MaskwaSam/GridMazePlatform/reference/photos/IMG_6221-preview.jpg

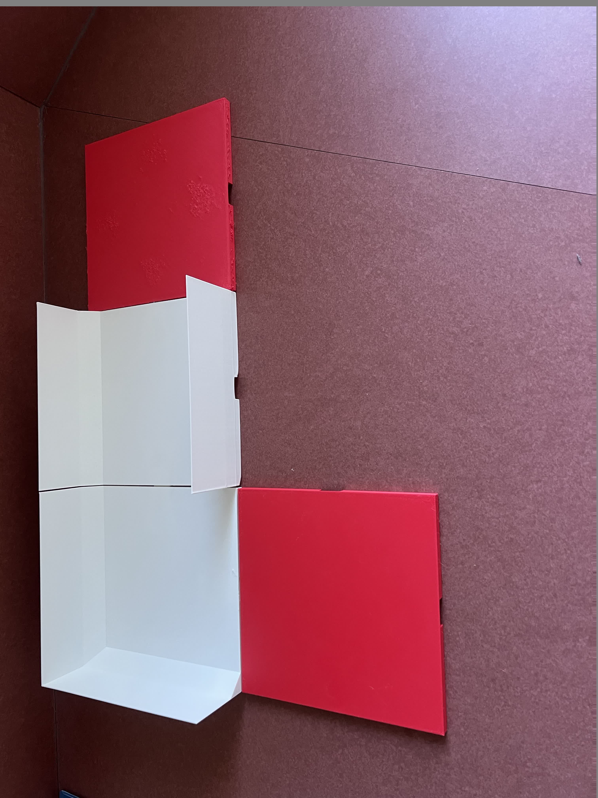
reference/photos/IMG_6221-preview.jpg
