MaskwaSam/GridMazePlatform/docs/images/h2d-wall-45deg-transition.png

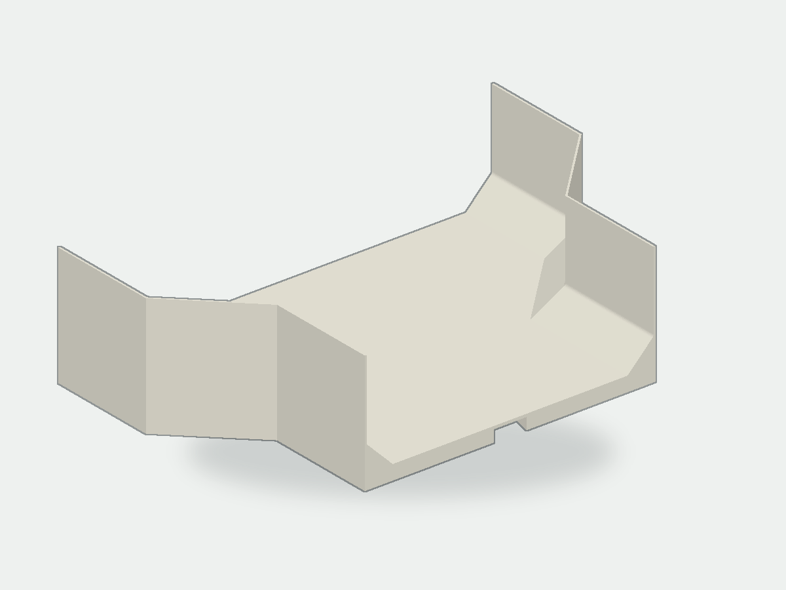
docs/images/h2d-wall-45deg-transition.png
