MaskwaSam/GridMazePlatform/docs/images/h2d-wall-200x300-end.png

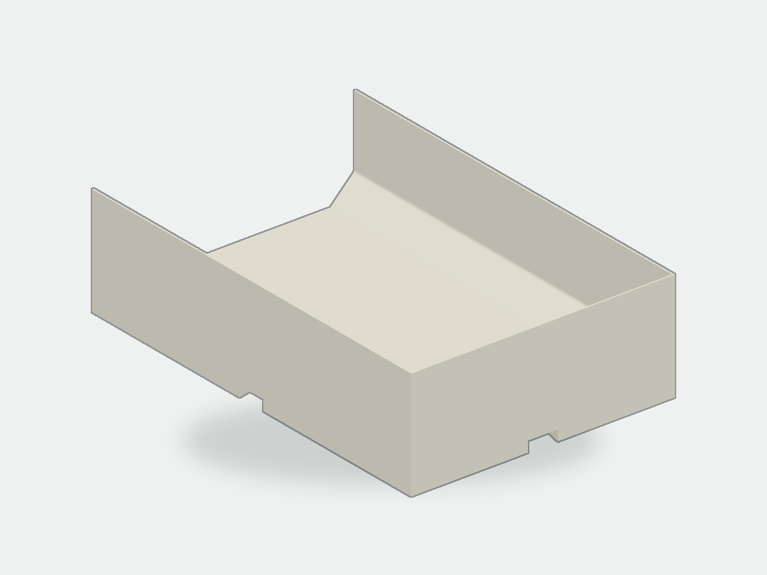
docs/images/h2d-wall-200x300-end.png
