MaskwaSam/GridMazePlatform/docs/images/h2d-wall-300x300-45deg-four-way-clean.png

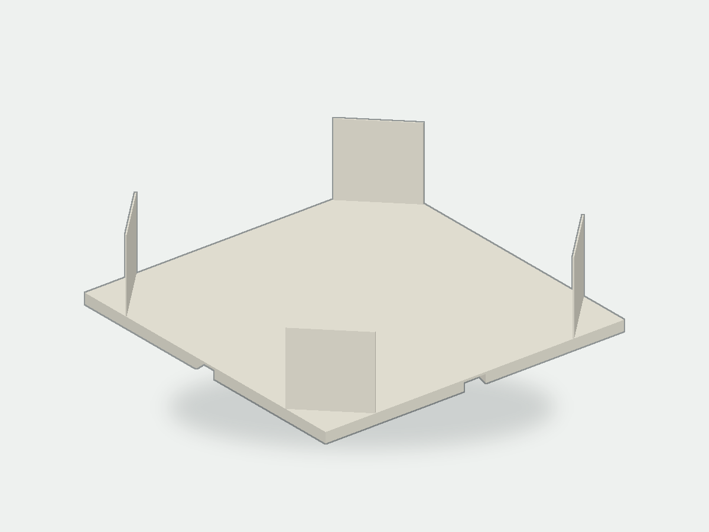
docs/images/h2d-wall-300x300-45deg-four-way-clean.png
