MaskwaSam/GridMazePlatform/docs/images/h2d-wall-300x300-end.png

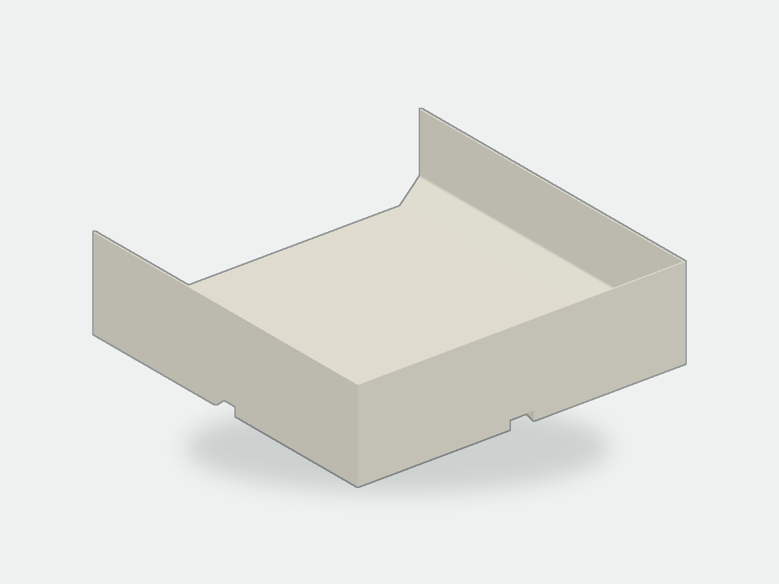
docs/images/h2d-wall-300x300-end.png
