MaskwaSam/GridMazePlatform/docs/images/h2d-wall-300x300-t-junction.png

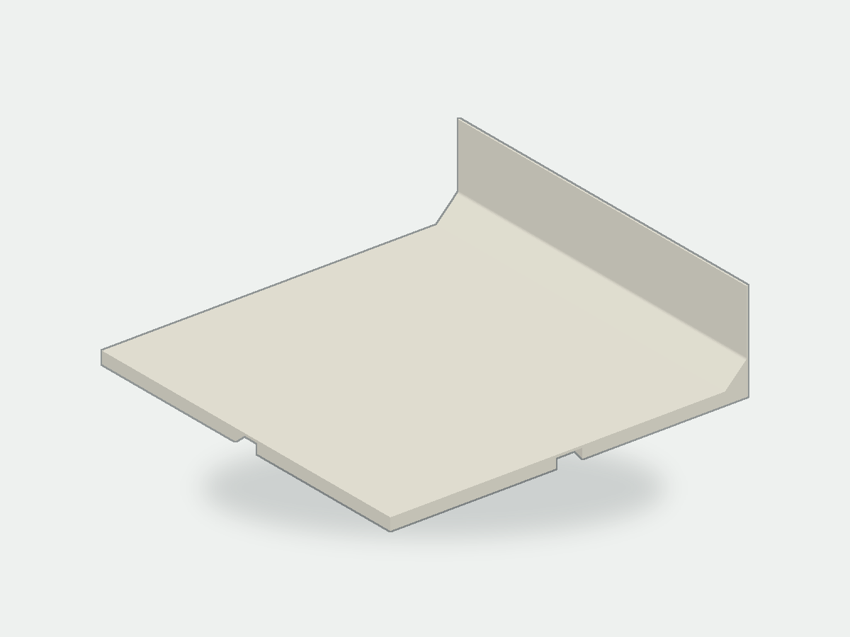
docs/images/h2d-wall-300x300-t-junction.png
