MaskwaSam/GridMazePlatform/docs/images/maze-piece-corner.png

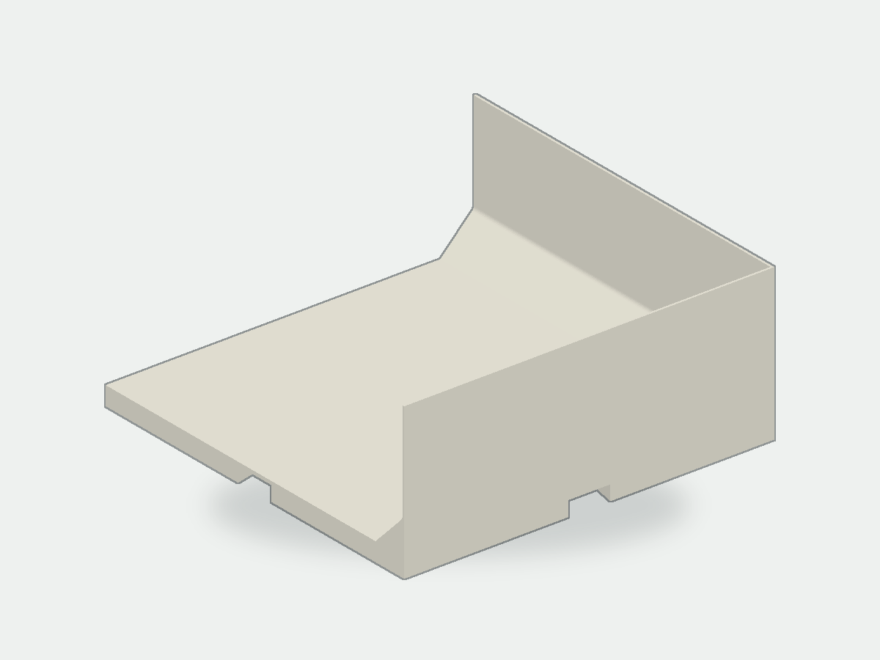
docs/images/maze-piece-corner.png
