MaskwaSam/GridMazePlatform/docs/images/maze-piece-end.png

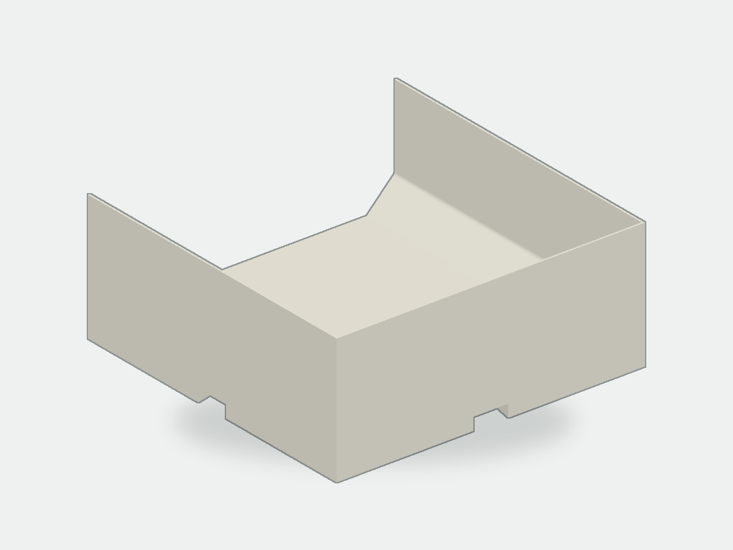
docs/images/maze-piece-end.png
