MaskwaSam/GridMazePlatform/docs/images/maze-piece-h2d-200x300-30deg-up-down-ramp.png

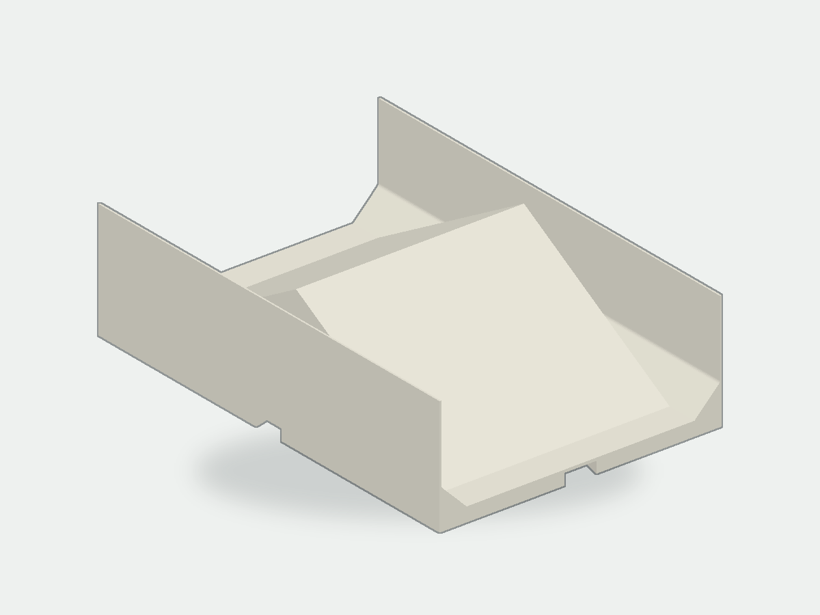
docs/images/maze-piece-h2d-200x300-30deg-up-down-ramp.png
