MaskwaSam/GridMazePlatform/docs/images/maze-piece-h2d-200x300-offset-ridge.png

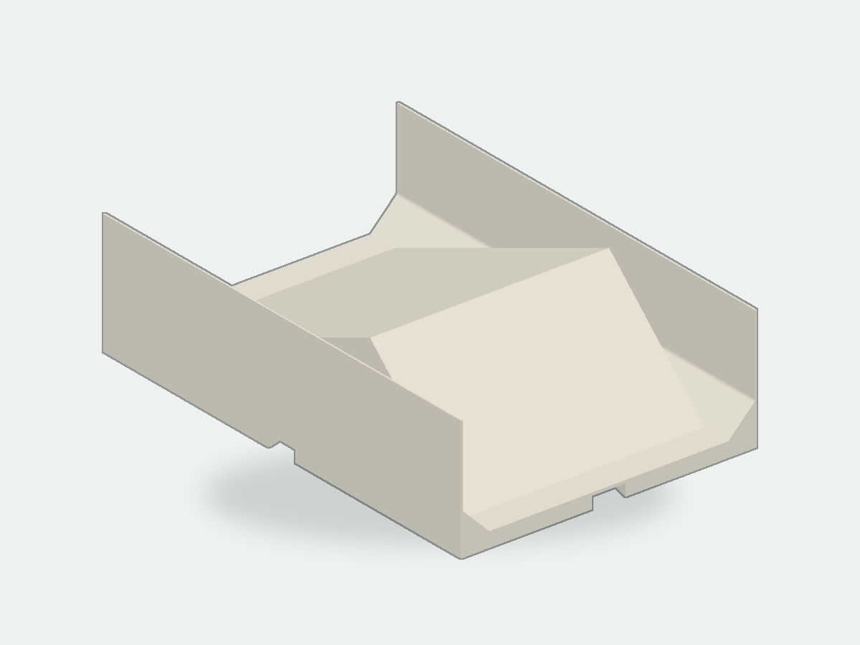
docs/images/maze-piece-h2d-200x300-offset-ridge.png
