MaskwaSam/GridMazePlatform/docs/images/maze-piece-h2d-200x300-single-wall-ridge.png

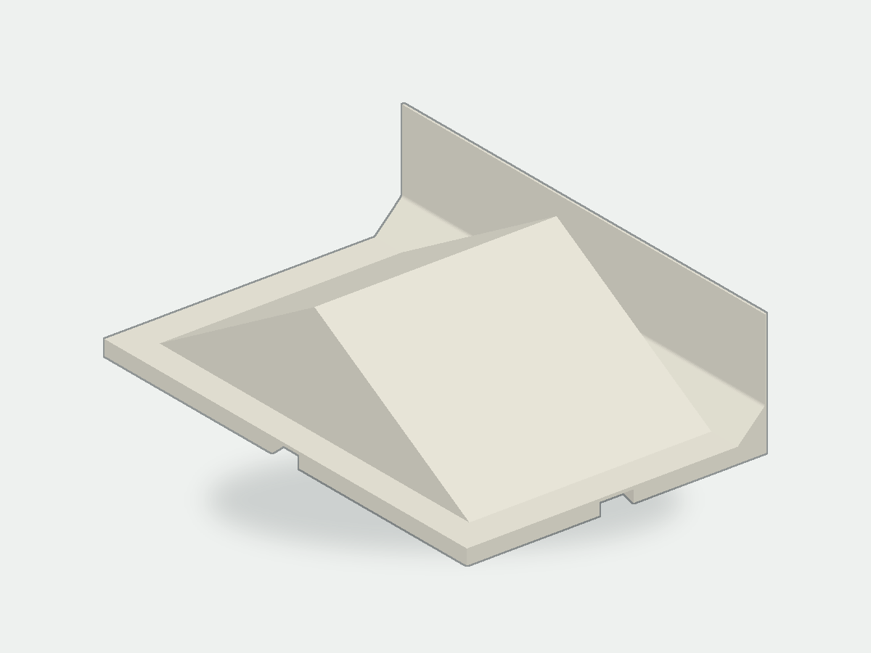
docs/images/maze-piece-h2d-200x300-single-wall-ridge.png
