MaskwaSam/GridMazePlatform/docs/images/maze-piece-straight.png

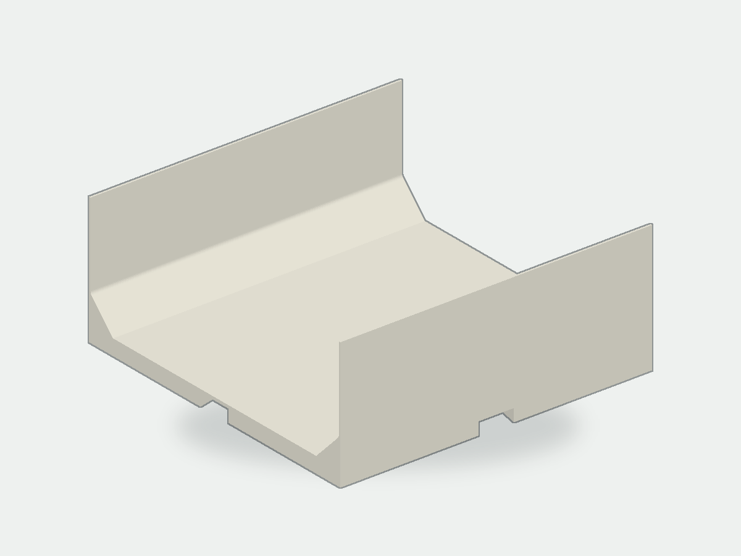
docs/images/maze-piece-straight.png
