MaskwaSam/GridMazePlatform/docs/images/maze-piece-x1c-200x200-30deg-ramp.png

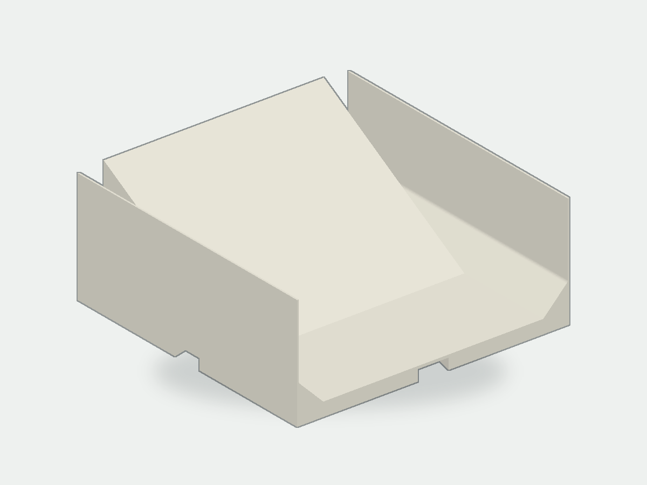
docs/images/maze-piece-x1c-200x200-30deg-ramp.png
