MaskwaSam/GridMazePlatform/output/variants/maze_piece_end_v1.stl

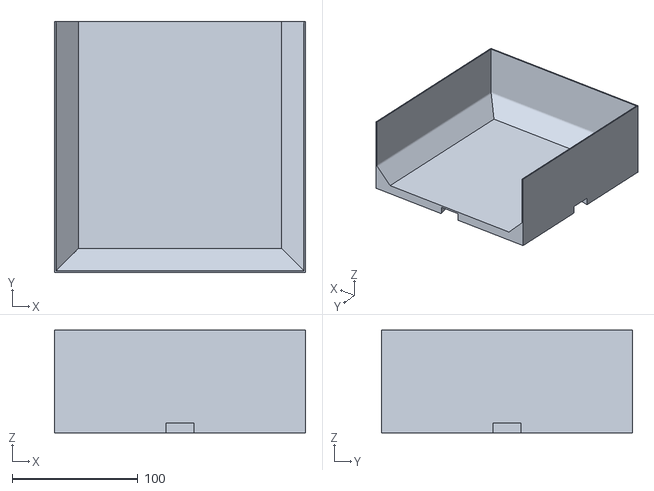
[picture p35: CAD file, 2026-08-30]
output/variants/maze_piece_end_v1.stl
200.0 x 200.0 x 82.0
