MaskwaSam/GridMazePlatform/output/h2d-wall-variants/maze_piece_h2d_200x300_t_junction_v1.stl

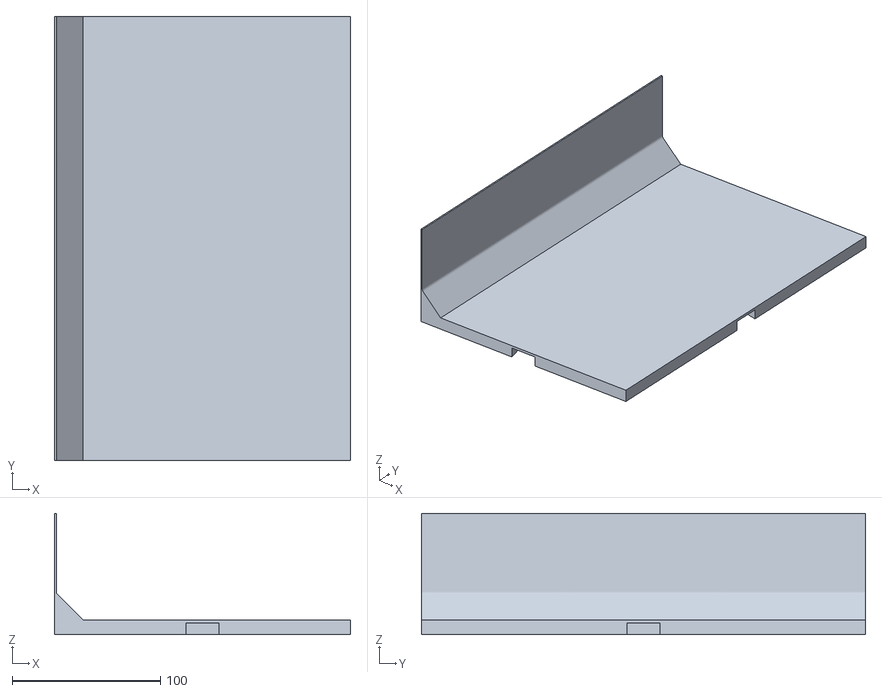
[picture p36: CAD file, 2026-09-28]
output/h2d-wall-variants/maze_piece_h2d_200x300_t_junction_v1.stl
200.0 x 300.0 x 82.0
