MaskwaSam/GridMazePlatform/output/challenge-ramp-variants/maze_piece_h2d_200x300_double_hump_30mm_rise_v1.stl

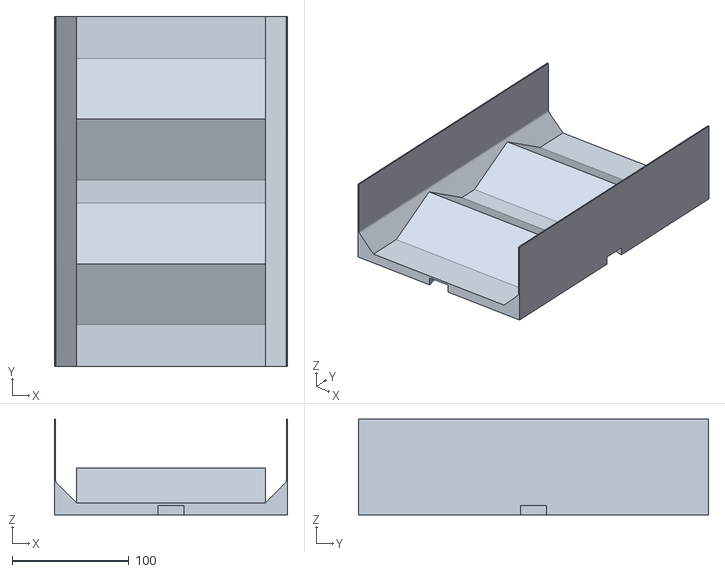
[picture p37: CAD file, 2026-09-28]
output/challenge-ramp-variants/maze_piece_h2d_200x300_double_hump_30mm_rise_v1.stl
200.0 x 300.0 x 82.0
