MaskwaSam/GridMazePlatform/output/h2d-wall-variants/maze_piece_h2d_300x300_corner_v1.stl

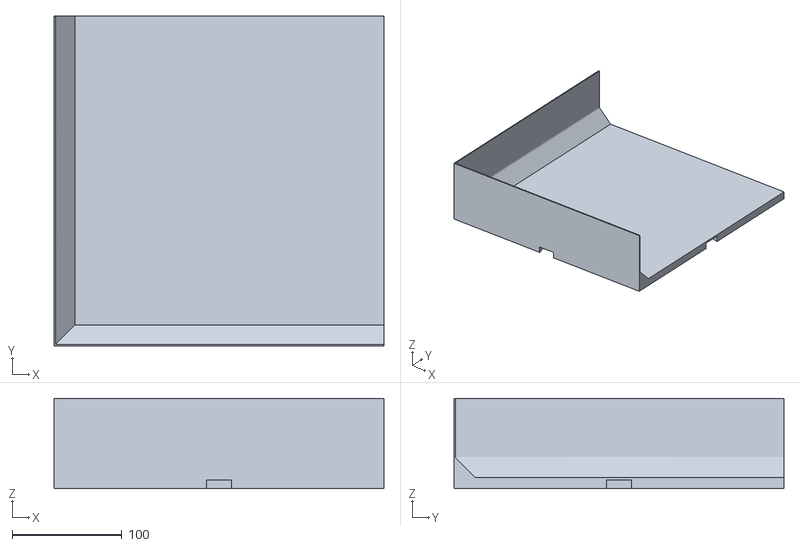
[picture p38: CAD file, 2026-09-28]
output/h2d-wall-variants/maze_piece_h2d_300x300_corner_v1.stl
300.0 x 300.0 x 82.0
