MaskwaSam/GridMazePlatform/output/challenge-ramp-variants/maze_piece_h2d_200x300_open_sides_ridge_v1.stl

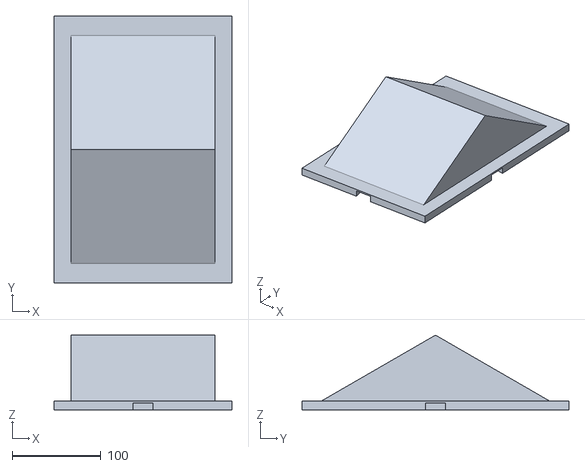
[picture p40: CAD file, 2026-09-28]
output/challenge-ramp-variants/maze_piece_h2d_200x300_open_sides_ridge_v1.stl
200.0 x 300.0 x 84.0
